jdistlr/garden-torch-connector/docs/desktop-workbench-20261001.jpg

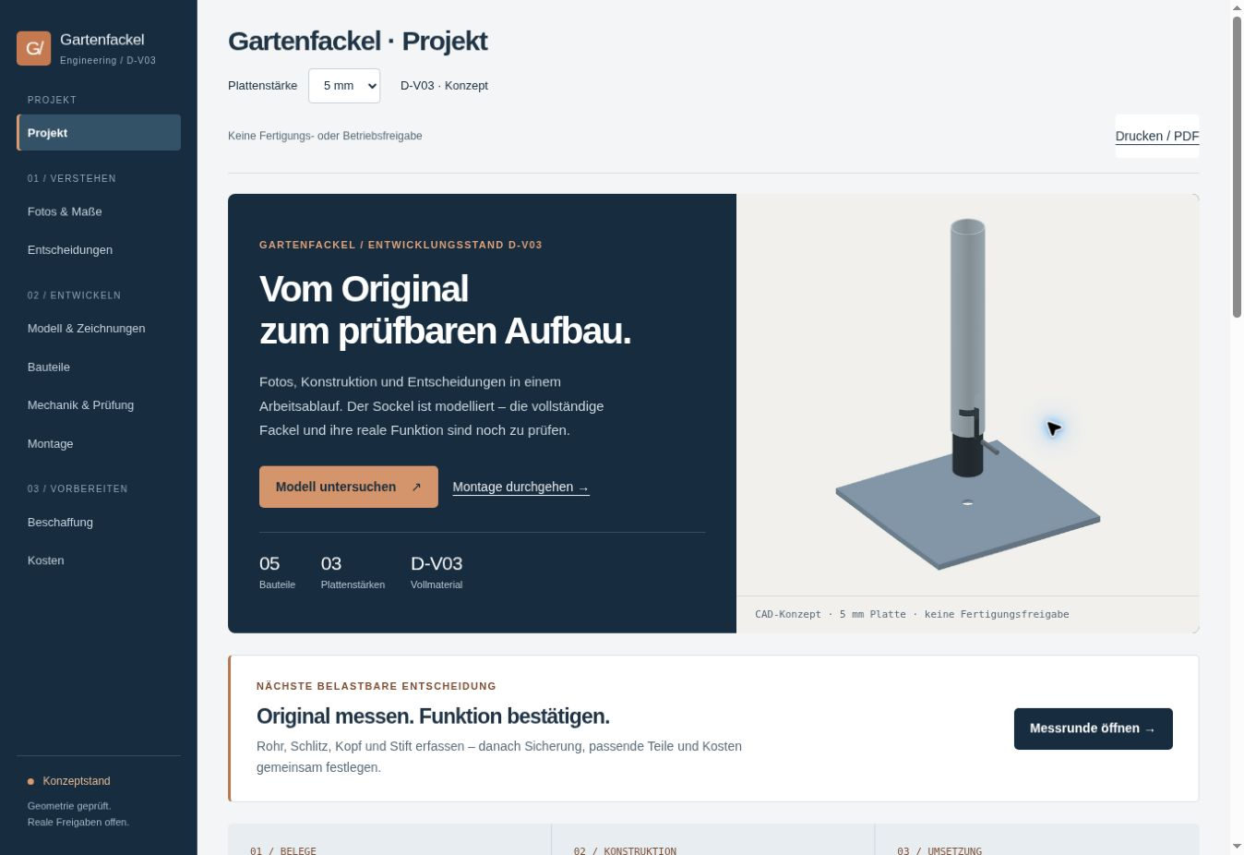
docs/desktop-workbench-20261001.jpg
