jdistlr/garden-torch-connector/docs/projekt-integration-mobile.jpg

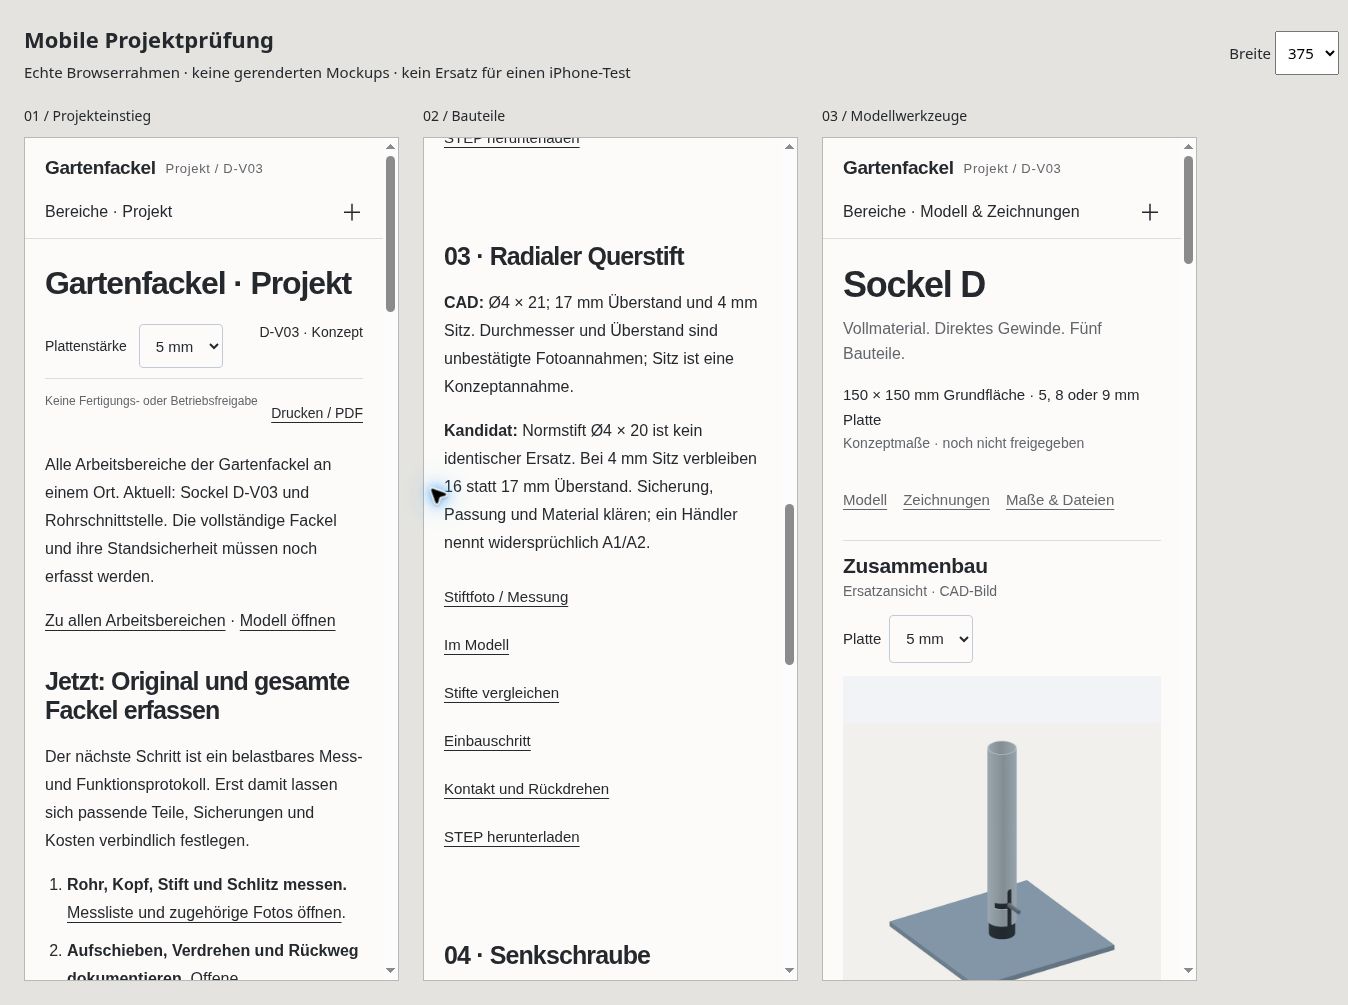
docs/projekt-integration-mobile.jpg
