jdistlr/garden-torch-connector/docs/ux-mobile-review.jpg

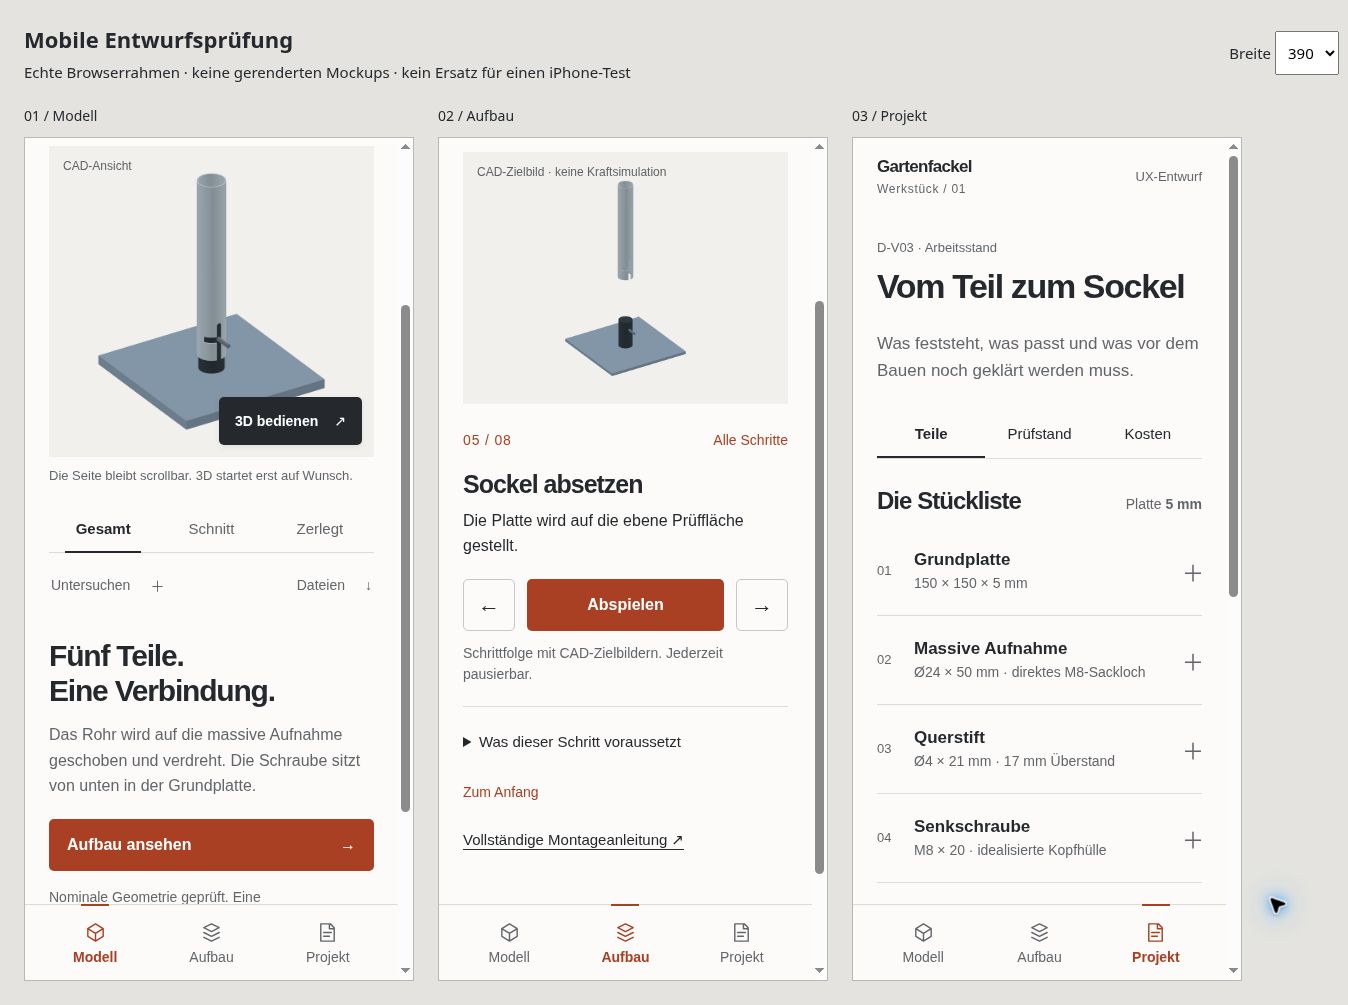
docs/ux-mobile-review.jpg
