jdistlr/garden-torch-connector/docs/xray-demo-proof-20261001.jpg

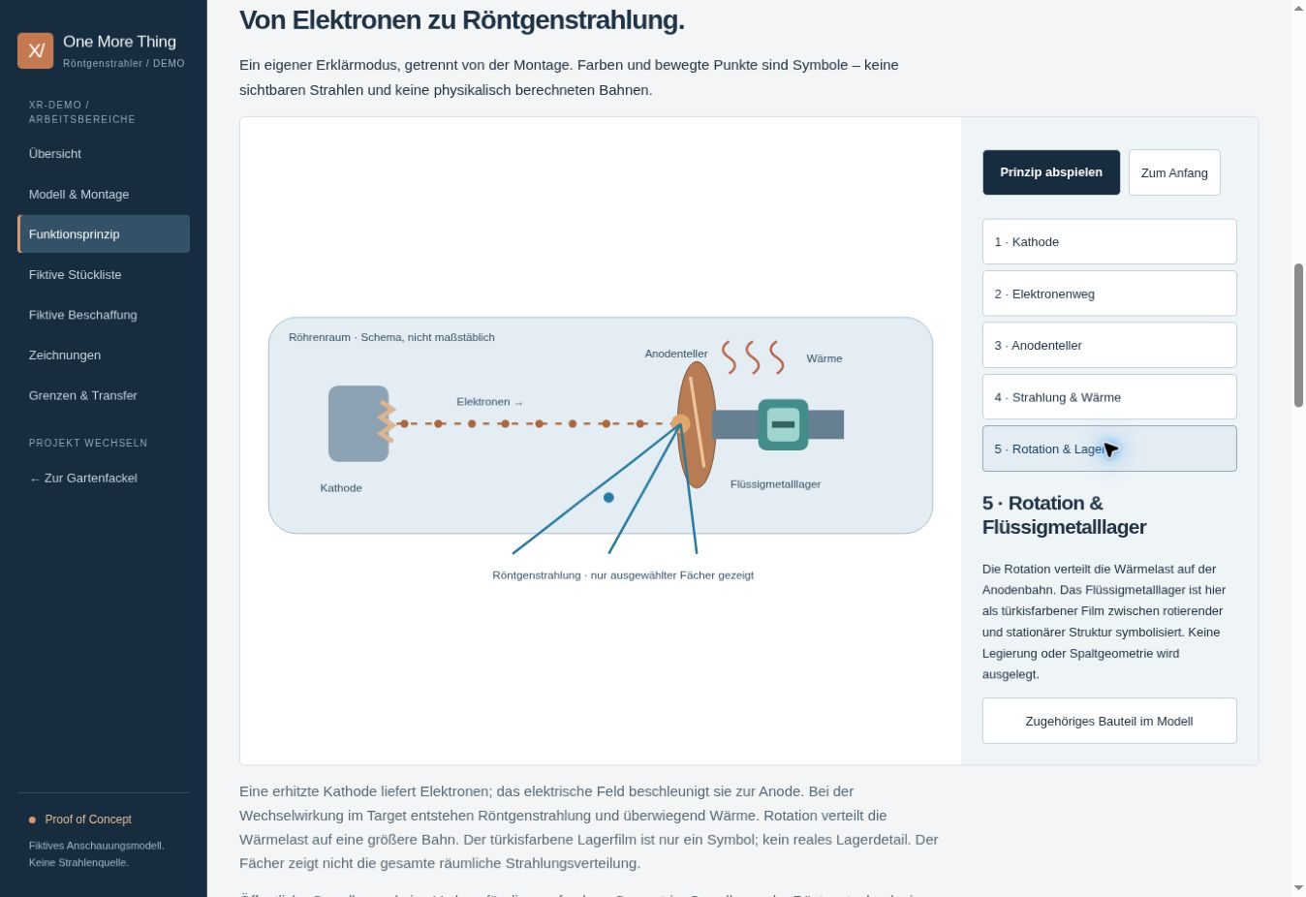
docs/xray-demo-proof-20261001.jpg
