jdistlr/garden-torch-connector/web/assets/sockel-d/blatt-5-1.png

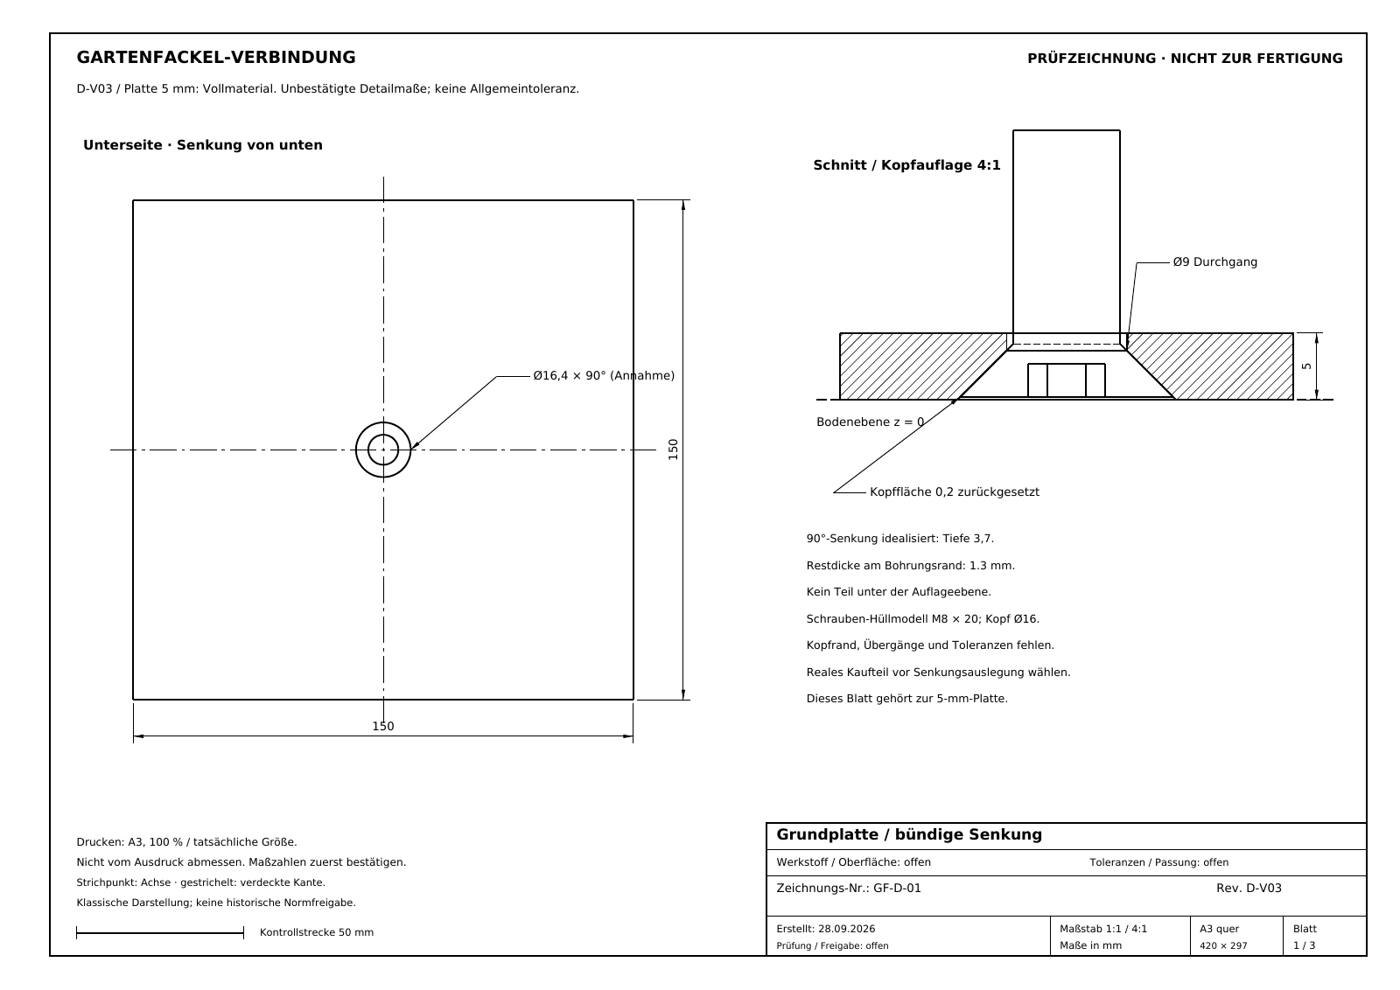
web/assets/sockel-d/blatt-5-1.png
