jdistlr/garden-torch-connector/web/assets/sockel-d/blatt-5-2.png

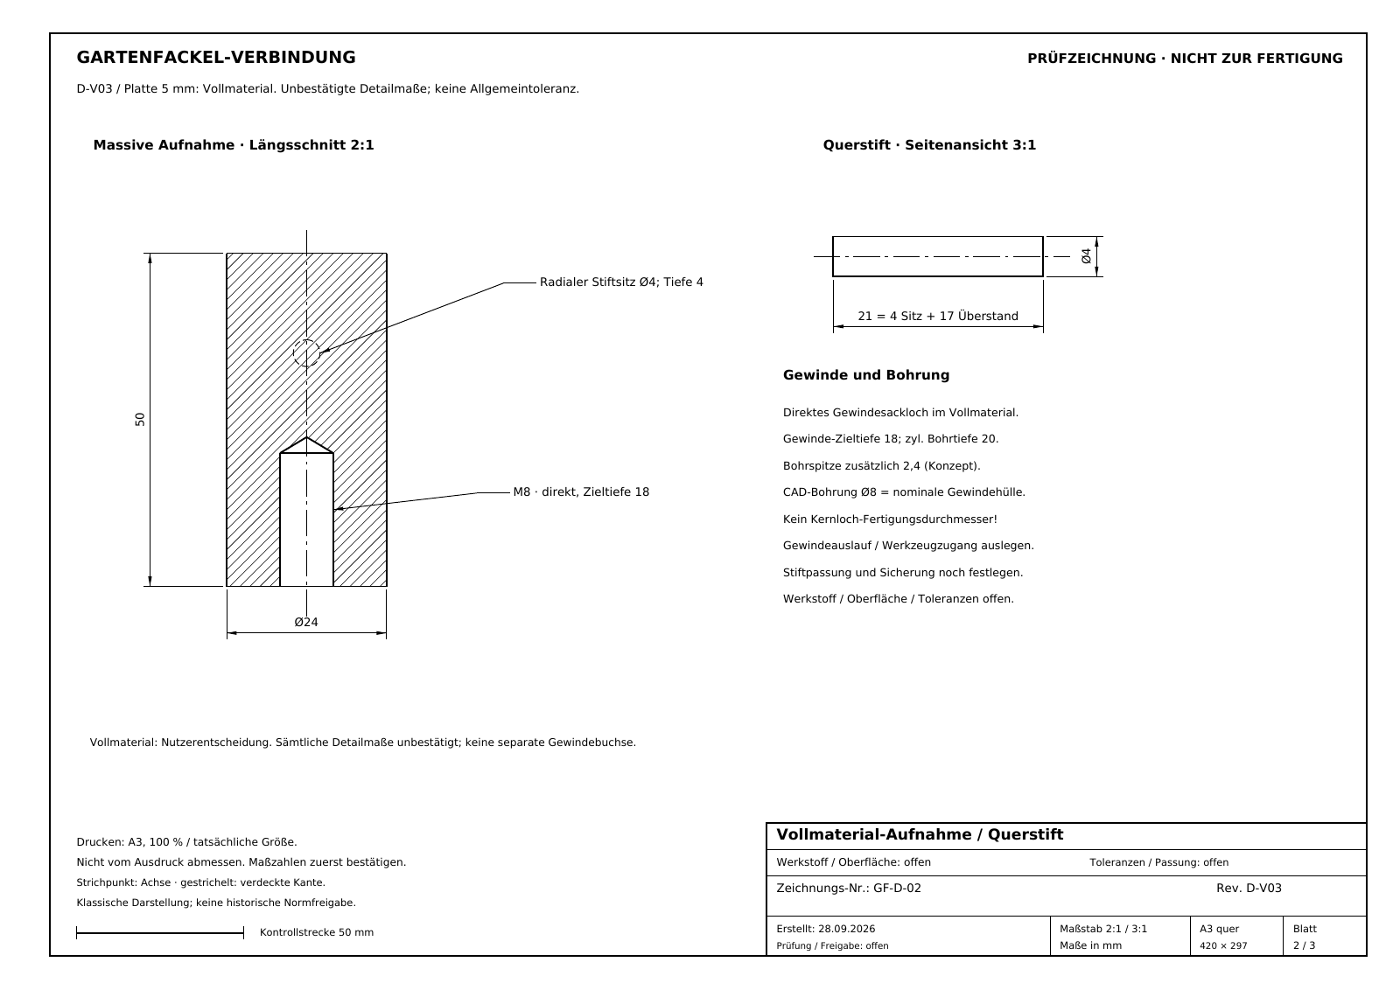
web/assets/sockel-d/blatt-5-2.png
