jdistlr/garden-torch-connector/web/assets/sockel-d/blatt-5-3.png

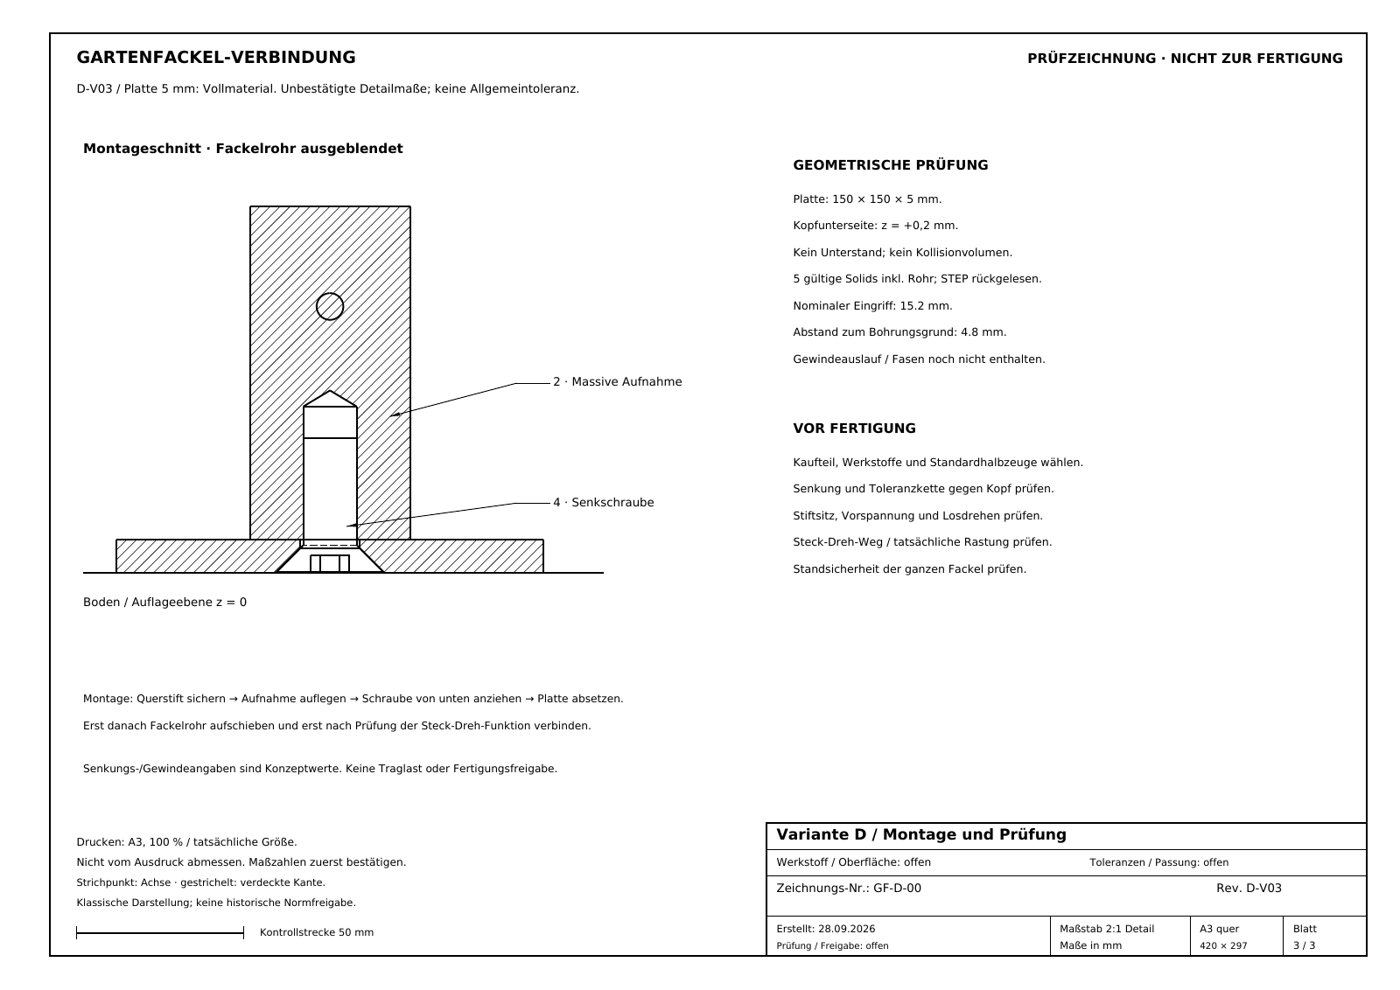
web/assets/sockel-d/blatt-5-3.png
