jdistlr/garden-torch-connector/web/assets/ux/exploded-5.png

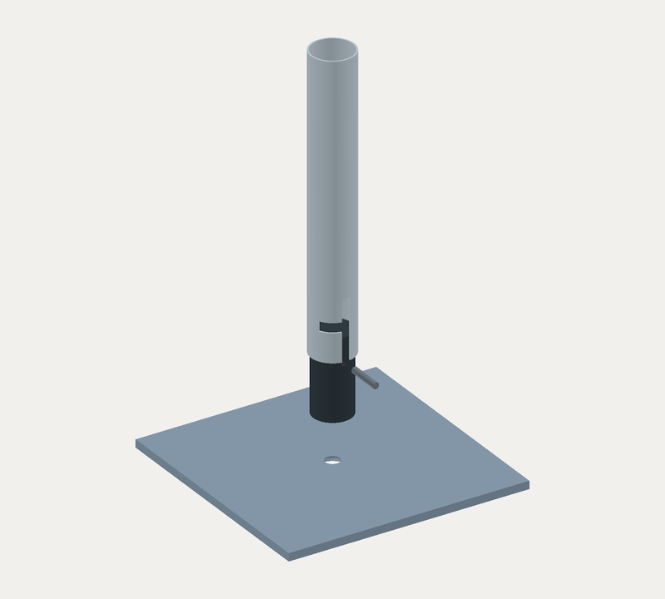
web/assets/ux/exploded-5.png
