jdistlr/garden-torch-connector/web/assets/ux/section-5.png

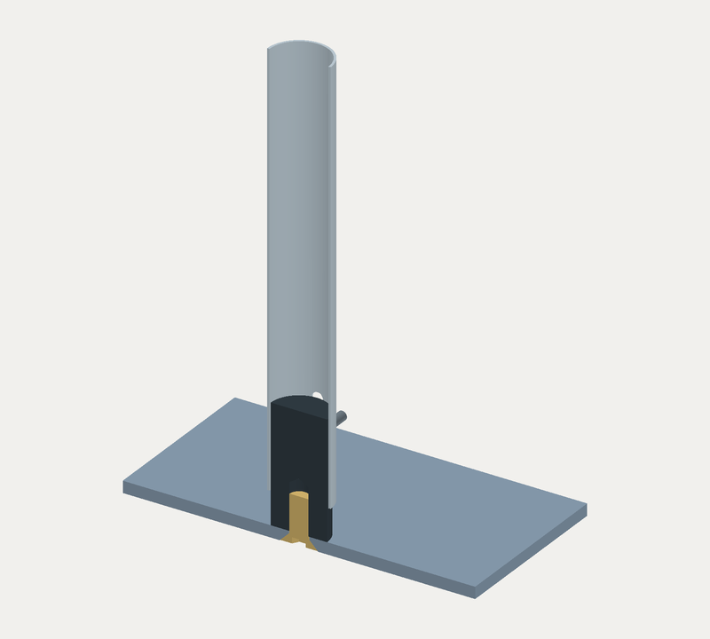
web/assets/ux/section-5.png
