jdistlr/garden-torch-connector/web/assets/zeichnung-D02-1.png

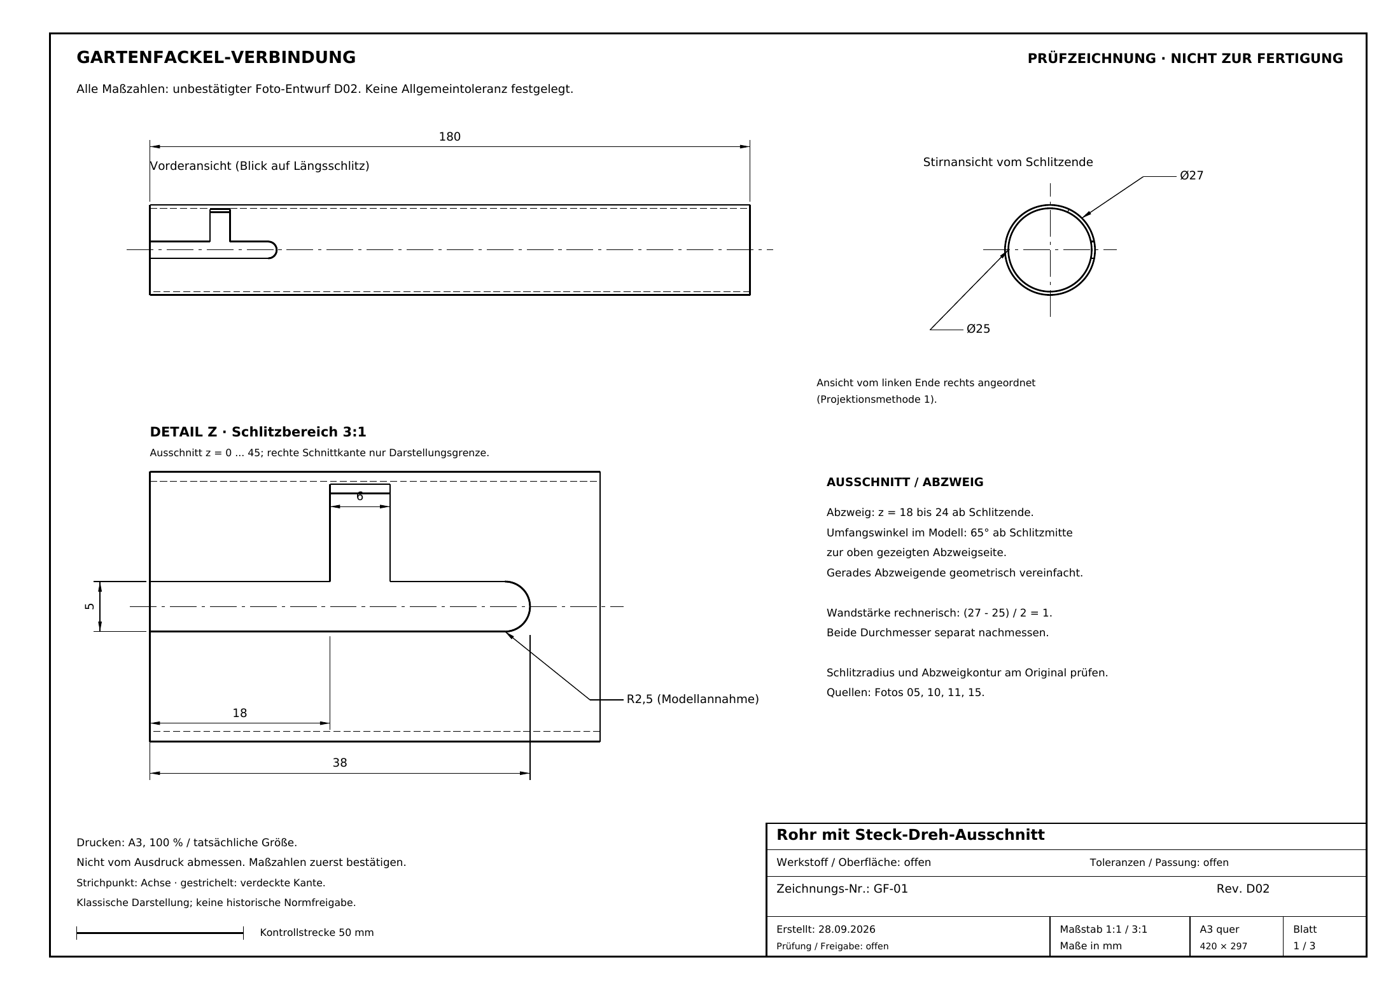
web/assets/zeichnung-D02-1.png
