jdistlr/garden-torch-connector/web/assets/zeichnung-D02-2.png

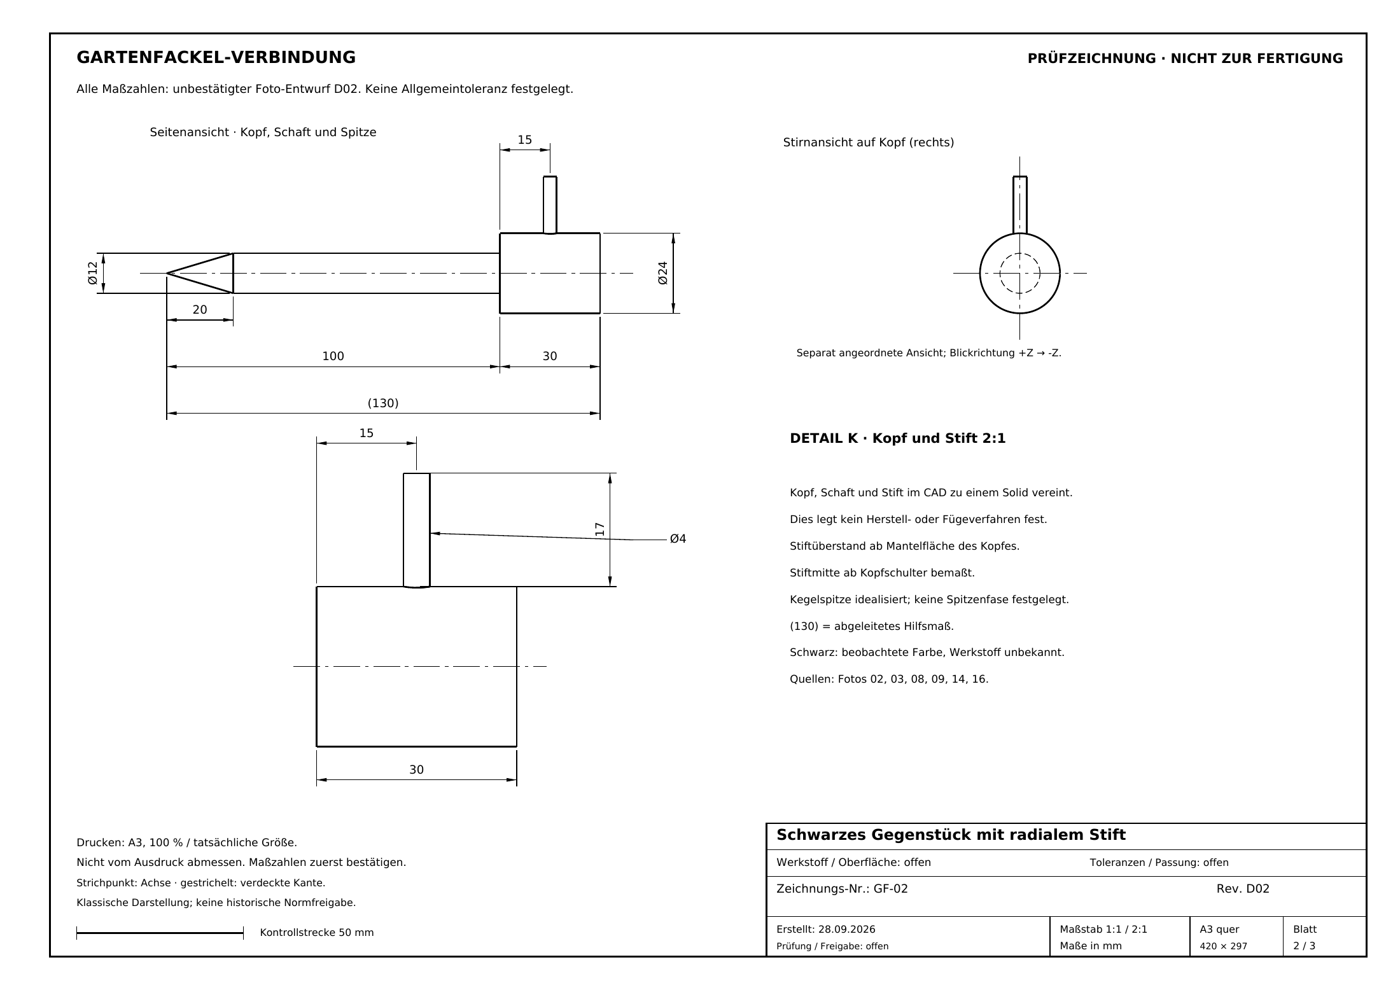
web/assets/zeichnung-D02-2.png
