jdistlr/garden-torch-connector/web/assets/zeichnung-D02-3.png

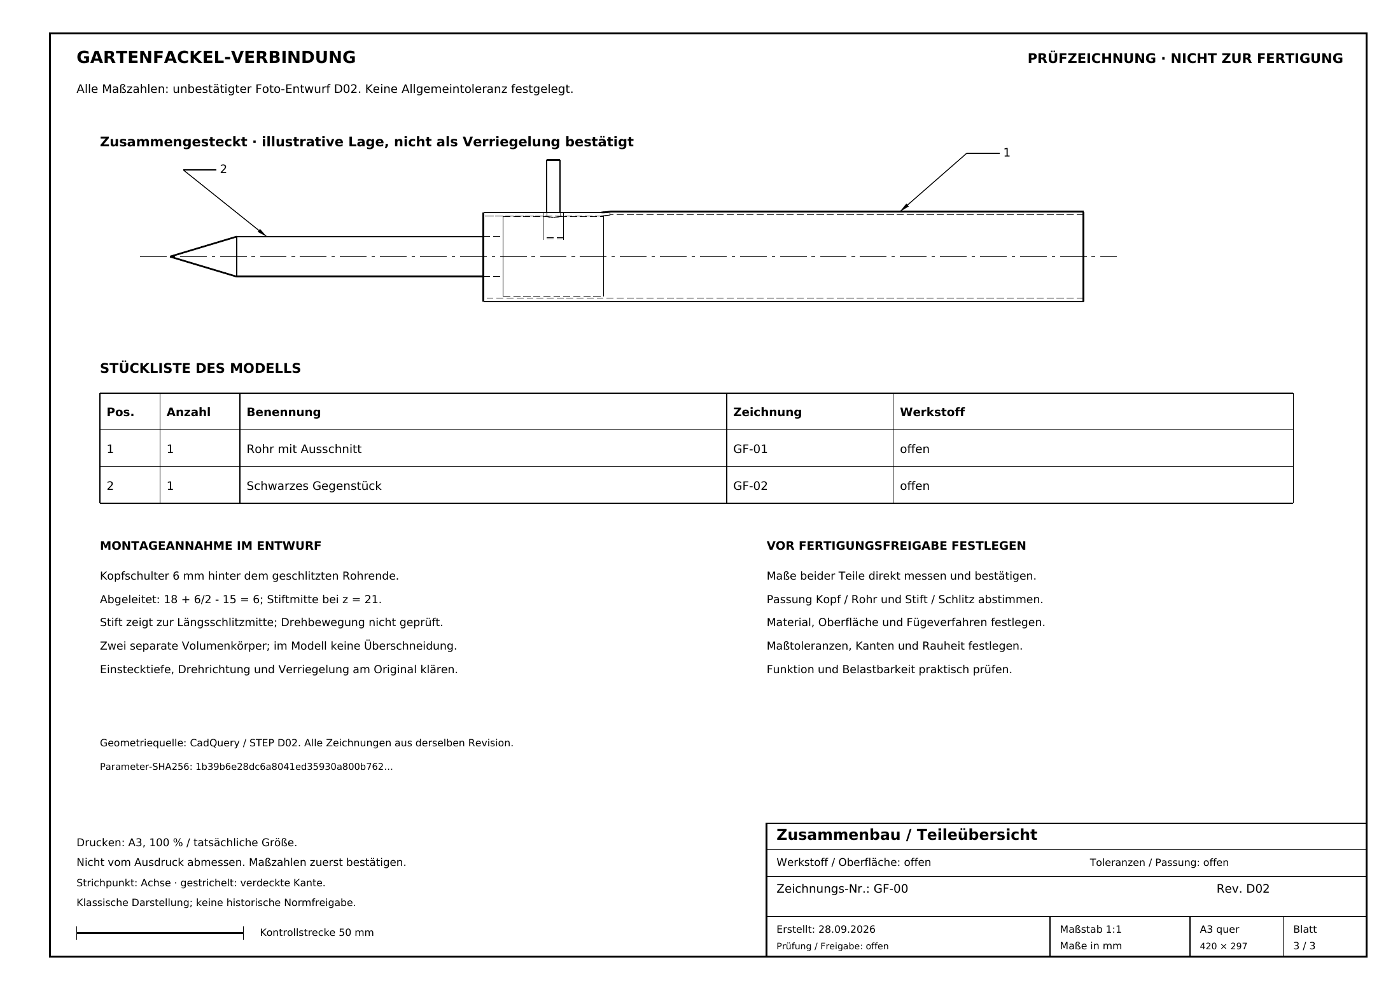
web/assets/zeichnung-D02-3.png
