jdistlr/garden-torch-connector/web/assets/variants/A-concept.step

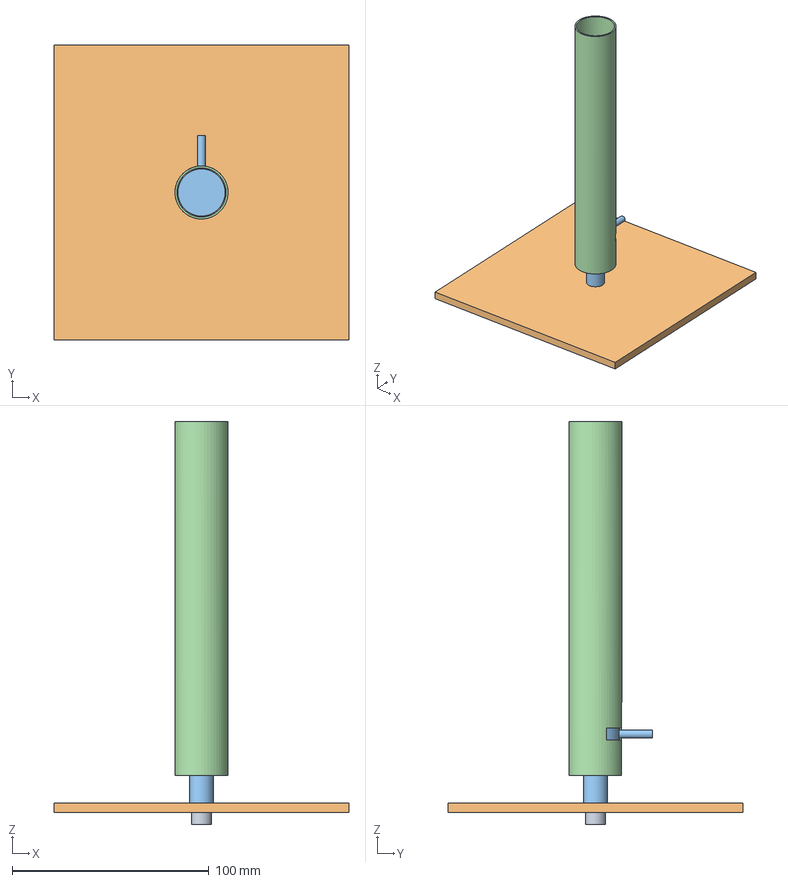
[picture p41: CAD file, 2026-09-28]
web/assets/variants/A-concept.step
150.0 x 150.0 x 205.0 mm
