jdistlr/garden-torch-connector/web/assets/xray-demo/cover.stl

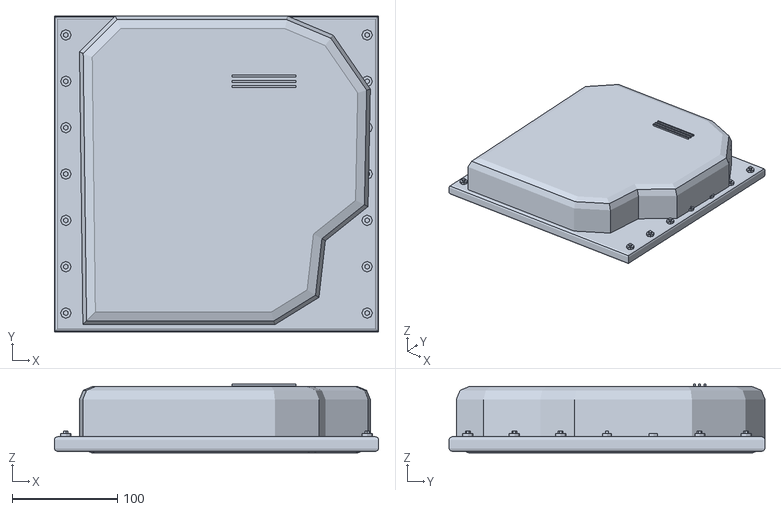
[picture p42: CAD file, 2026-10-01]
web/assets/xray-demo/cover.stl
308.0 x 300.0 x 65.5
