jdistlr/garden-torch-connector/web/assets/variants/C-concept.step

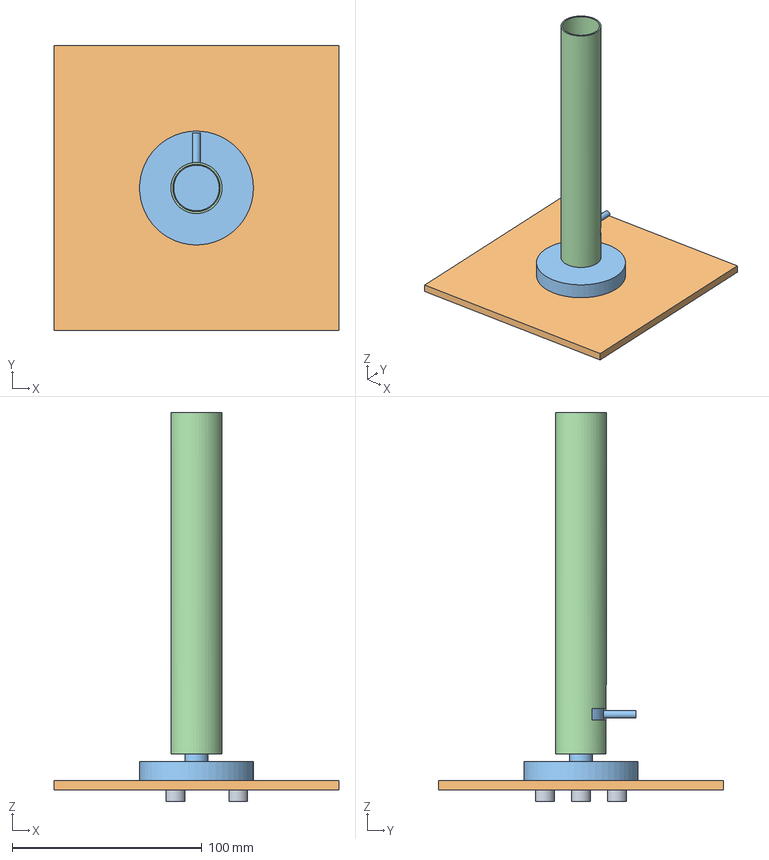
[picture p43: CAD file, 2026-09-28]
web/assets/variants/C-concept.step
150.0 x 150.0 x 205.0 mm
