jdistlr/garden-torch-connector/web/assets/xray-demo/bearing.stl

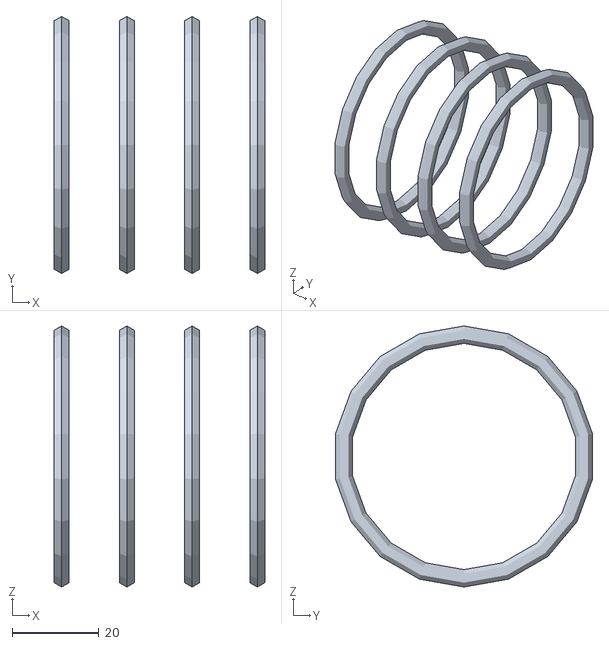
[picture p44: CAD file, 2026-10-01]
web/assets/xray-demo/bearing.stl
48.5 x 59.1 x 60.0
