jdistlr/garden-torch-connector/web/assets/xray-demo/envelope.stl

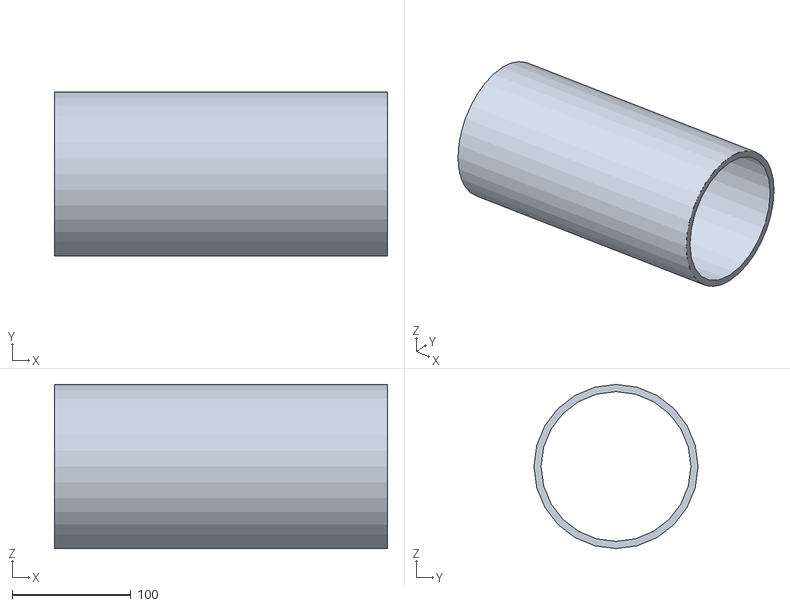
[picture p45: CAD file, 2026-10-01]
web/assets/xray-demo/envelope.stl
280.0 x 138.0 x 138.0
