jdistlr/garden-torch-connector/web/assets/xray-demo/endcap.stl

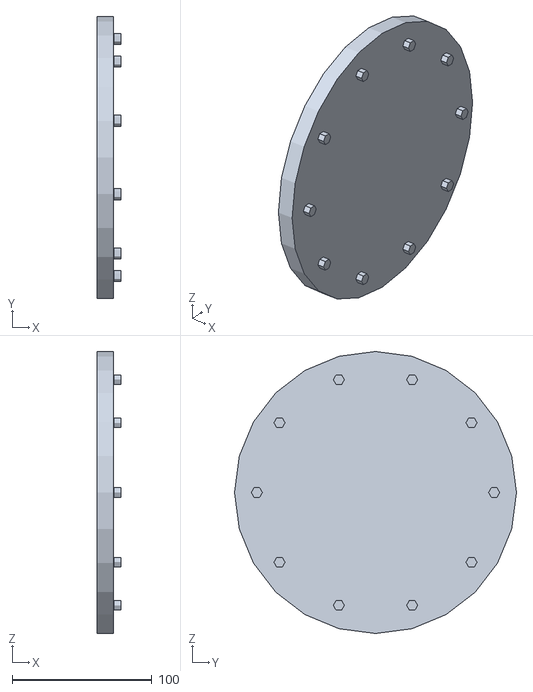
[picture p46: CAD file, 2026-10-01]
web/assets/xray-demo/endcap.stl
17.5 x 202.0 x 202.0
