jdistlr/garden-torch-connector/web/assets/xray-demo/anode.stl

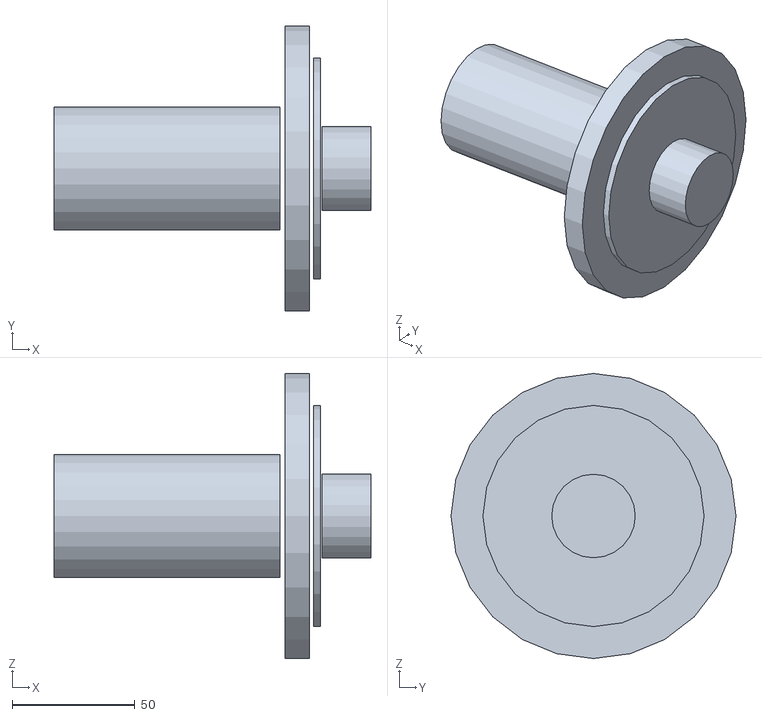
[picture p47: CAD file, 2026-10-01]
web/assets/xray-demo/anode.stl
129.0 x 116.0 x 116.0
