jdistlr/garden-torch-connector/web/assets/xray-demo/base.stl

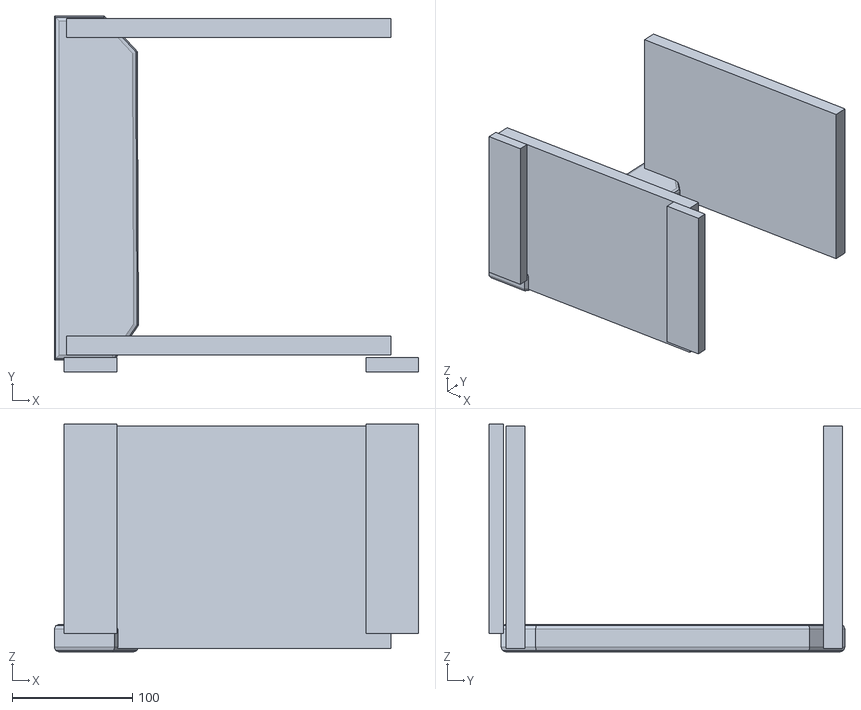
[picture p48: CAD file, 2026-10-01]
web/assets/xray-demo/base.stl
303.0 x 296.0 x 189.5
