jdistlr/garden-torch-connector/web/assets/xray-demo/housing.stl

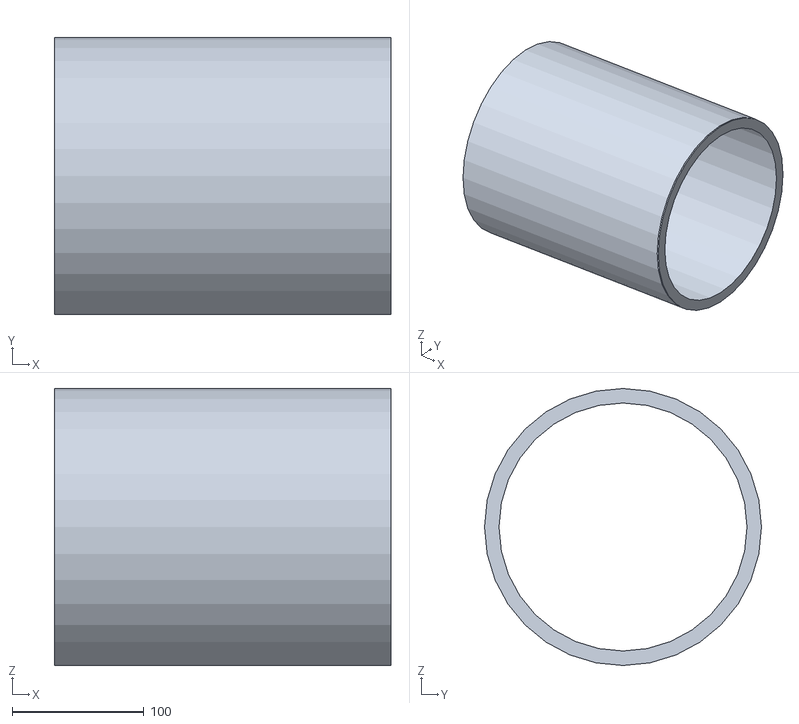
[picture p49: CAD file, 2026-10-01]
web/assets/xray-demo/housing.stl
257.0 x 210.0 x 210.0
