jdistlr/garden-torch-connector/web/assets/sockel-d/plate-5.step

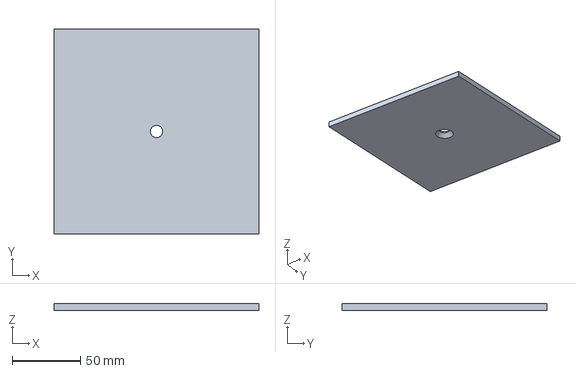
[picture p50: CAD file, 2026-09-28]
web/assets/sockel-d/plate-5.step
150.0 x 150.0 x 5.00 mm
