jdistlr/garden-torch-connector/web/assets/xray-demo/carrier.stl

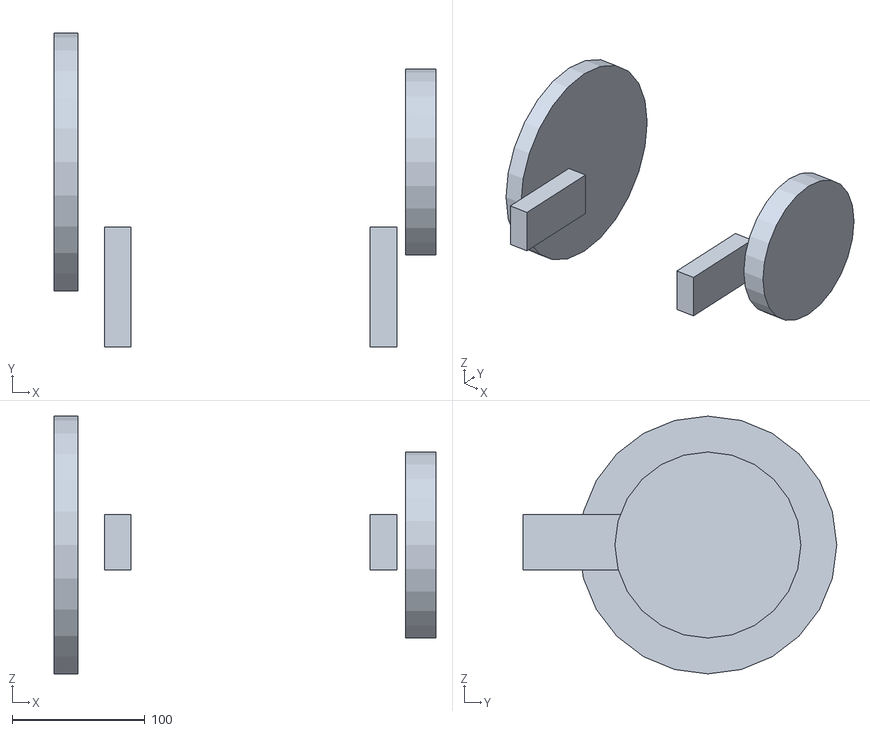
[picture p51: CAD file, 2026-10-01]
web/assets/xray-demo/carrier.stl
287.5 x 236.0 x 194.0
