jdistlr/garden-torch-connector/web/assets/xray-demo/cooler.stl

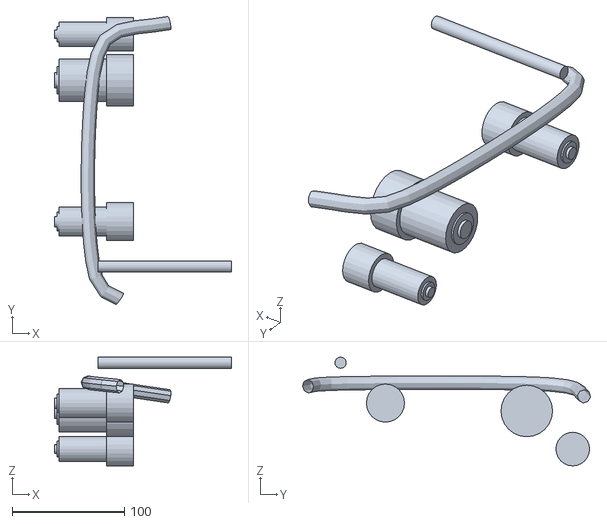
[picture p52: CAD file, 2026-10-01]
web/assets/xray-demo/cooler.stl
158.0 x 256.8 x 97.0
