jdistlr/garden-torch-connector/web/assets/sockel-d/adapter-5.step

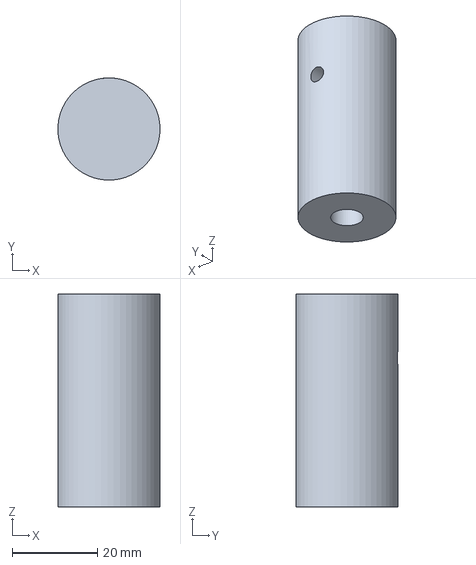
[picture p53: CAD file, 2026-09-28]
web/assets/sockel-d/adapter-5.step
24.0 x 24.0 x 50.0 mm
