jdistlr/garden-torch-connector/web/assets/ux/step-0-5.png

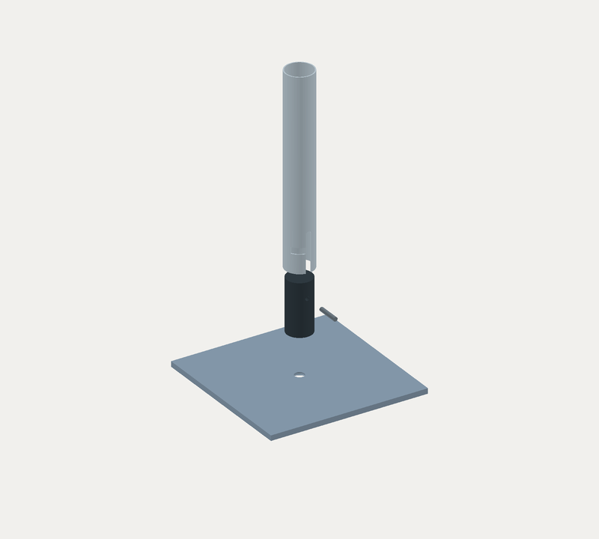
web/assets/ux/step-0-5.png
