jdistlr/garden-torch-connector/web/assets/ux/step-4-5.png

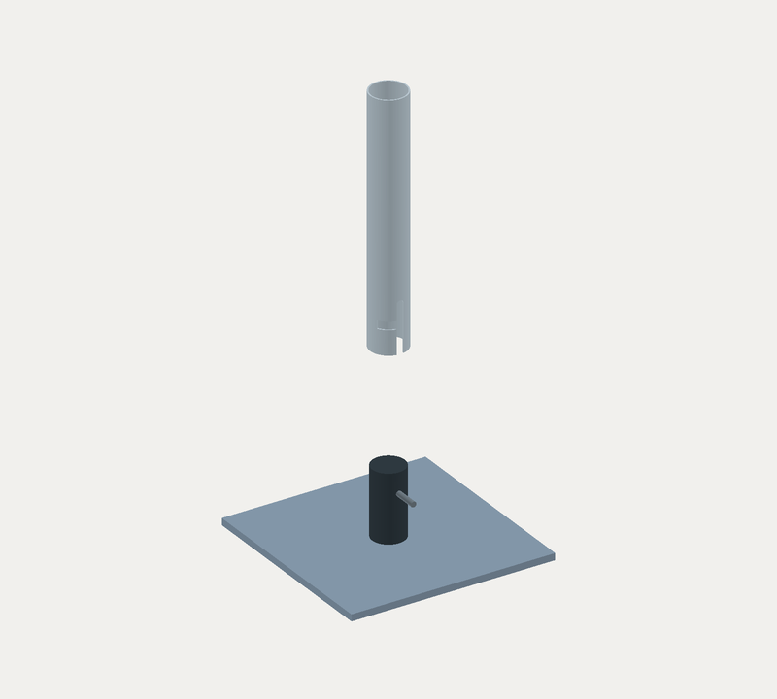
web/assets/ux/step-4-5.png
